LauraMWerneck/Projeto_Integrador_3/Etapa 1/Aplicativo/README.md

# Metodologia para criar o Aplicativo 

Usar um microcontrolador ESP com backend em Python e frontend em HTML resulta em soluções eficazes e escaláveis, unindo o poder do hardware à flexibilidade do software. 

Ao integrar um backend em Python, você se beneficia de uma linguagem versátil e fácil de usar, ideal para manipulação de dados e desenvolvimento de APIs. O Python possui diversas bibliotecas que facilitam a comunicação com o microcontrolador, permitindo o recebimento e processamento de dados em tempo real.

Por outro lado, um frontend em HTML oferece uma interface amigável e acessível, permitindo que usuários interajam facilmente com o sistema. A combinação de um backend robusto em Python com um frontend em HTML proporciona uma experiência fluida e intuitiva, permitindo que você visualize dados, controle dispositivos e crie dashboards personalizados.

Parte da interface do frontend do projeto já foi desenvolvido. No entanto, o backend ainda está em fase de planejamento e será criado assim que começarem os testes com o microcontrolador ESP. 

Essa abordagem permite que a equipe valide a comunicação e o desempenho do hardware antes de integrar a lógica do backend. Uma vez que os testes estejam em andamento e os dados do microcontrolador sejam obtidos, o backend em Python será implementado para gerenciar esses dados, possibilitando uma comunicação eficiente entre o frontend e o microcontrolador. Assim, garantimos que toda a estrutura esteja alinhada e otimizada para oferecer a melhor experiência possível.

## Referências:

RED HAT. O que são interfaces de programação de aplicativos? Disponível em: <https://www.redhat.com/pt-br/topics/api/what-are-application-programming-interfaces>.

MOZILLA DEVELOPER NETWORK. Noções básicas de HTML. Disponível em: <https://developer.mozilla.org/pt-BR/docs/Learn/Getting_started_with_the_web/HTML_basics>.
