LauraMWerneck/Projeto_Integrador_3/Projeto Final/Placa/Projeto Placa PI3/Placa_PI3.kicad_sch

## KiCad design Projeto Final/Placa/Projeto Placa PI3/Placa_PI3.kicad_sch (2025-02-10)

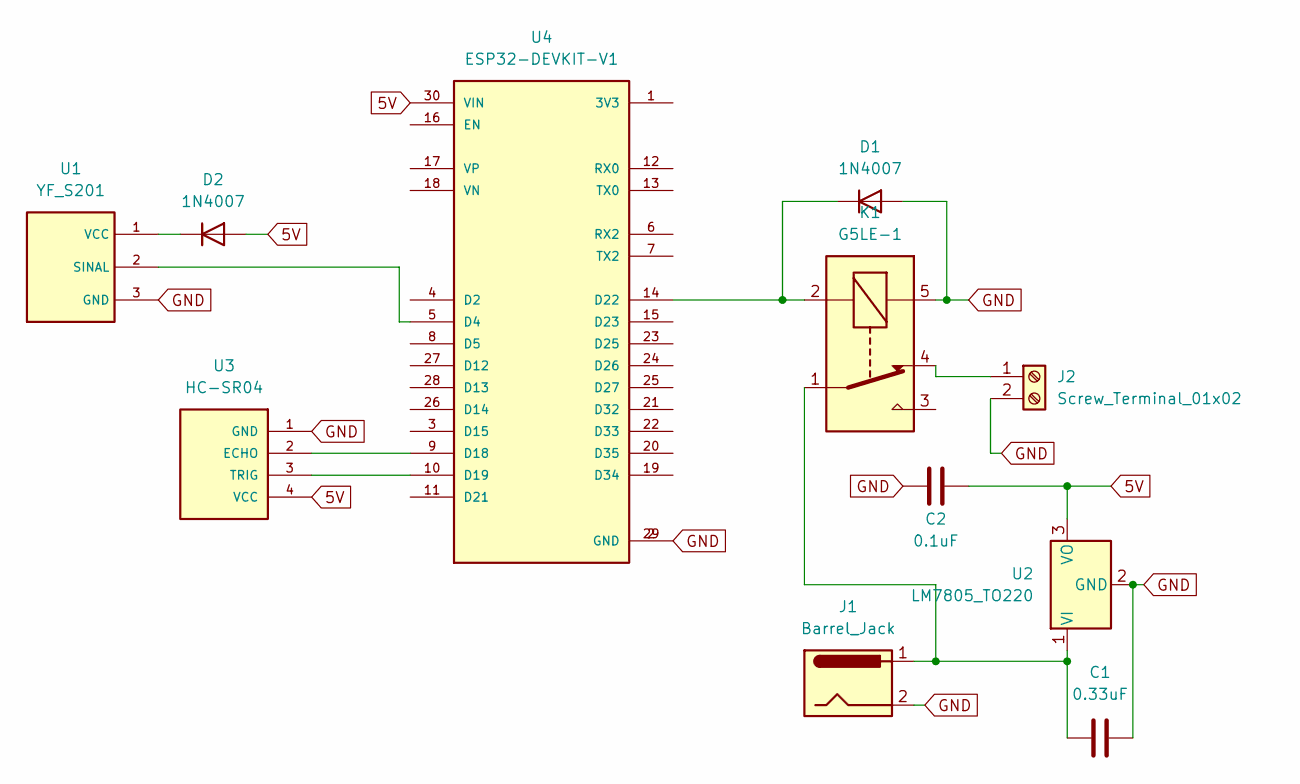
[picture p9: schematic Placa_PI3.kicad_sch]

Parts:
C1: 0.33uF; C_Disc_D10.5mm_W5.0mm_P5.00mm
C2: 0.1uF; C_Disc_D10.5mm_W5.0mm_P5.00mm
D1, D2: 1N4007; D_DO-41_SOD81_P10.16mm_Horizontal
J1: Barrel_Jack; BarrelJack_Horizontal
J2: Screw_Terminal_01x02; TerminalBlock_MetzConnect_Type073_RT02602HBLU_1x02_P5.08mm_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
K1: G5LE-1; Relay_SPDT_Omron-G5LE-12
U1: YF_S201; PinHeader_1x03_P2.00mm_Vertical
U2: LM7805_TO220; TO-220-3_Vertical2
U3: HC-SR04; XCVR_HC-SR04
U4: ESP32-DEVKIT-V1; MODULE_ESP32_DEVKIT_V1; PARTREV N/A

Connections:
5V: C2.1, D2.2 (A), U2.3 (VO), U3.4 (VCC), U4.30 (VIN)
GND: C1.2, C2.2, D1.2 (A), J1.2, J2.2, K1.5, U1.3 (GND), U2.2 (GND), U3.1 (GND), U4.2 (GND), U4.29 (GND)
unnamed: C1.1, J1.1, K1.1, U2.1 (VI)
unnamed: D1.1 (K), K1.2, U4.14 (D22)
unnamed: D2.1 (K), U1.1 (VCC)
unnamed: J2.1, K1.4
unnamed: U1.2 (SINAL), U4.5 (D4)
unnamed: U3.2 (ECHO), U4.9 (D18)
unnamed: U3.3 (TRIG), U4.10 (D19)
